joe-sq/Memory-Game-on-Arduino/PCB-design-KiCAD/PCB design.kicad_sch

## KiCad design PCB-design-KiCAD/PCB design.kicad_sch (2026-05-20)

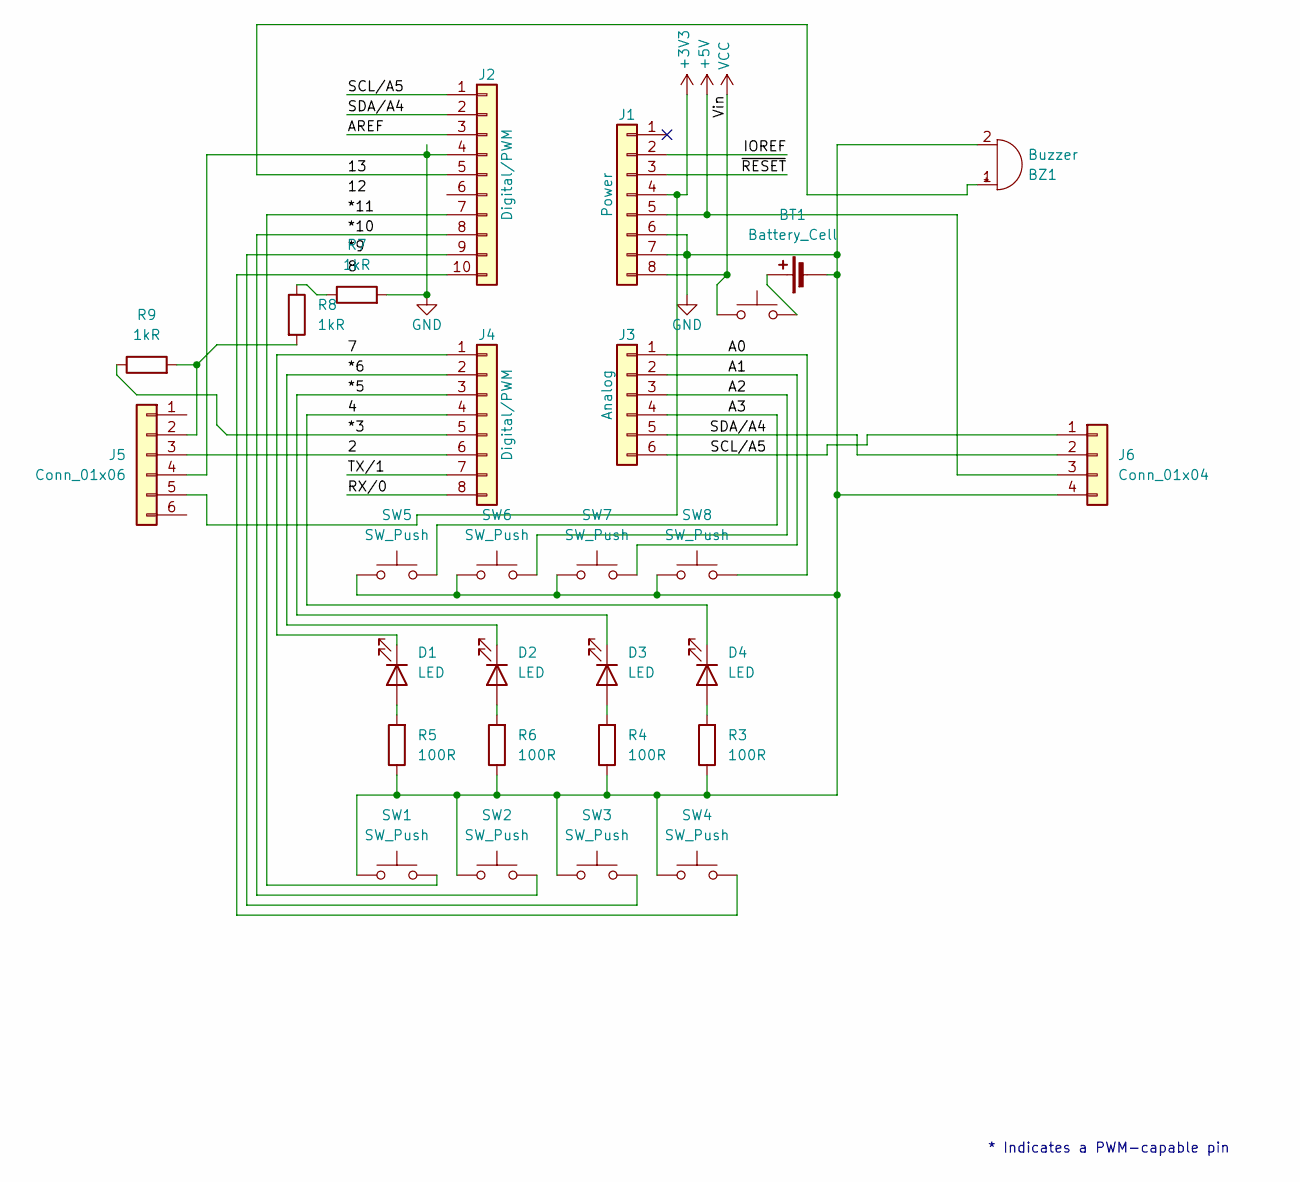
[picture p2: schematic PCB design.kicad_sch]

Parts:
BT1: Battery_Cell; BatteryHolder_Keystone_1060_1x2032
BZ1: Buzzer; Buzzer_12x9.5RM7.6
D1, D2, D3, D4: LED; LED_Rectangular_W3.0mm_H2.0mm
J1: Power; PinSocket_1x08_P2.54mm_Vertical
J2: Digital/PWM; PinSocket_1x10_P2.54mm_Vertical
J3: Analog; PinSocket_1x06_P2.54mm_Vertical
J4: Digital/PWM; PinSocket_1x08_P2.54mm_Vertical
J5: Conn_01x06; PinHeader_1x06_P1.00mm_Vertical
J6: Conn_01x04; PinHeader_1x04_P1.00mm_Vertical
R3, R4, R5, R6: 100R; R_Axial_DIN0204_L3.6mm_D1.6mm_P7.62mm_Horizontal
R7, R8, R9: 1kR; R_Axial_DIN0204_L3.6mm_D1.6mm_P7.62mm_Horizontal
SW1, SW2, SW3, SW4, SW5, SW6, SW7, SW8: SW_Push; SW_PUSH-12mm
SW9: SW_Push; SW_Push_1P1T_NO_E-Switch_TL3301NxxxxxG

Connections:
2: J4.6, J5.3
3: J4.5, R9.1
4: D4.1 (K), J4.4
5: D3.1 (K), J4.3
6: D2.1 (K), J4.2
7: D1.1 (K), J4.1
8: J2.10, SW4.2
9: J2.9, SW3.2
10: J2.8, SW2.2
11: J2.7, SW1.2
13: BZ1.1 (+), J2.5
+3V3: J1.4, J5.5
+5V: J1.5, J6.3
A0: J3.1, SW8.2
A1: J3.2, SW7.2
A2: J3.3, SW6.2
A3: J3.4, SW5.2
AREF: J2.3
GND: BT1.2 (-), BZ1.2 (-), J1.6, J1.7, J2.4, J5.4, J6.4, R3.1, R4.1, R5.1, R6.1, R7.2, SW1.1, SW2.1, SW3.1, SW4.1, SW5.1, SW6.1, SW7.1, SW8.1
IOREF: J1.2
unnamed: BT1.1 (+), SW9.2
unnamed: D1.2 (A), R5.2
unnamed: D2.2 (A), R6.2
unnamed: D3.2 (A), R4.2
unnamed: D4.2 (A), R3.2
unnamed: J5.2, R8.2, R9.2
unnamed: R7.1, R8.1
RX/0: J4.8
SCL/A5: J2.1, J3.6, J6.1
SDA/A4: J2.2, J3.5, J6.2
TX/1: J4.7
VCC: J1.8, SW9.1
~RESET: J1.3

Notes on the sheet:
* Indicates a PWM-capable pin
